frankie-eight-days/10x-hardware-engineer/boards/imx6ull-devboard/hardware/src/parts/Q_J_CR2032_BS_6_1/BAT-SMD_L28.5-W16.0-H5.5-LS31.3_CR2032-BS-6-1.STEP

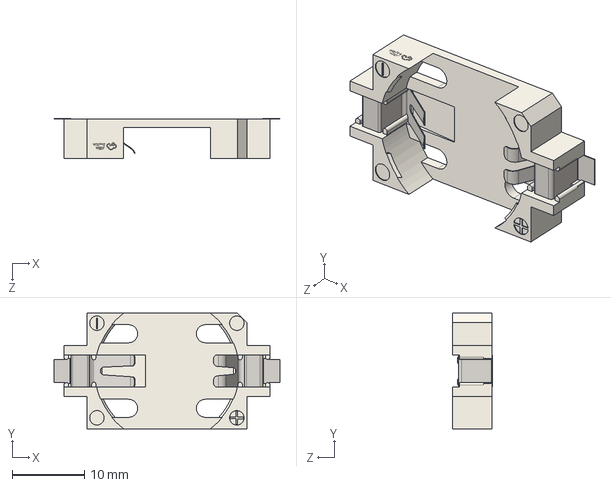
[picture p15: CAD file, 2026-05-05]
boards/imx6ull-devboard/hardware/src/parts/Q_J_CR2032_BS_6_1/BAT-SMD_L28.5-W16.0-H5.5-LS31.3_CR2032-BS-6-1.STEP
31.3 x 16.0 x 5.60 mm
