frankie-eight-days/10x-hardware-engineer/boards/imx6ull-devboard/hardware/src/parts/Samsung_Electro_Mechanics_CL21B102KBCNNNC/C0805_L2.0-W1.3-H1.3.step

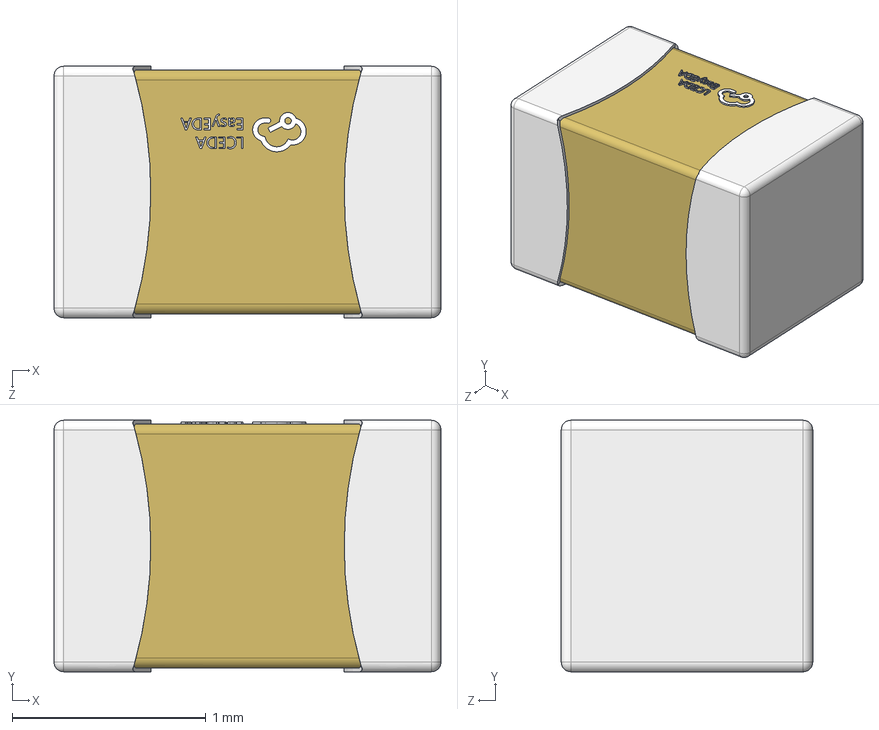
[picture p16: CAD file, 2026-05-05]
boards/imx6ull-devboard/hardware/src/parts/Samsung_Electro_Mechanics_CL21B102KBCNNNC/C0805_L2.0-W1.3-H1.3.step
2.00 x 1.30 x 1.30 mm
