frankie-eight-days/10x-hardware-engineer/boards/imx6ull-devboard/hardware/src/parts/Samsung_Electro_Mechanics_CL31A107MQHNNNE/C1206_L3.2-W1.6-H1.3.step

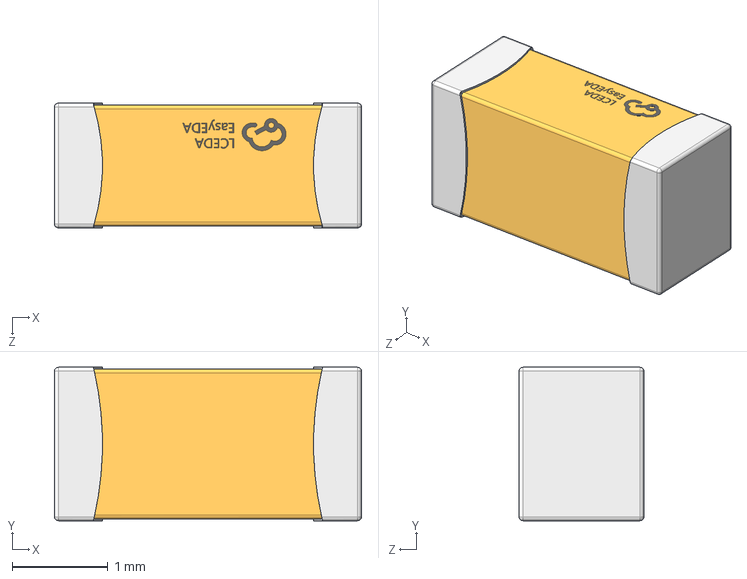
[picture p17: CAD file, 2026-05-05]
boards/imx6ull-devboard/hardware/src/parts/Samsung_Electro_Mechanics_CL31A107MQHNNNE/C1206_L3.2-W1.6-H1.3.step
3.20 x 1.60 x 1.30 mm
