frankie-eight-days/10x-hardware-engineer/boards/imx6ull-devboard/hardware/src/parts/Seiko_Epson_Q13FC13500004/FC-135R_L3.2-W1.5.STEP

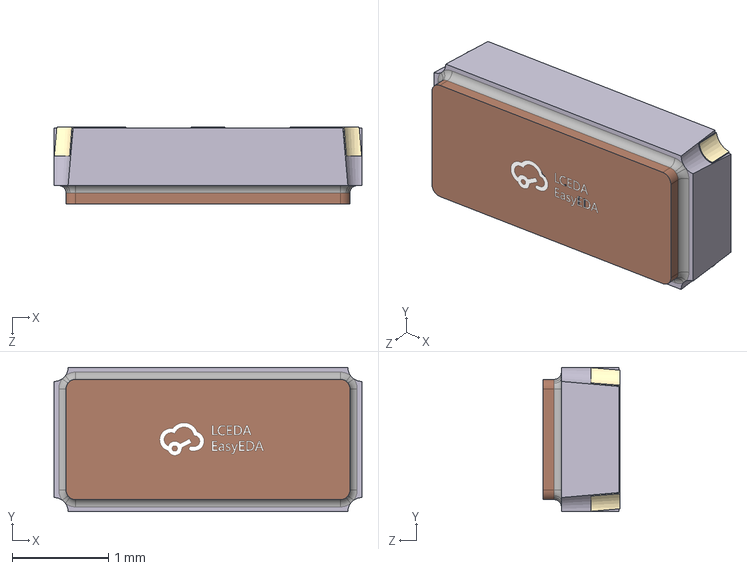
[picture p18: CAD file, 2026-05-05]
boards/imx6ull-devboard/hardware/src/parts/Seiko_Epson_Q13FC13500004/FC-135R_L3.2-W1.5.STEP
3.20 x 1.50 x 0.801 mm
