frankie-eight-days/10x-hardware-engineer/boards/imx6ull-devboard/hardware/src/parts/Sunlord_GZ2012D601TF/R0805_L2.0-W1.3-H0.6.step

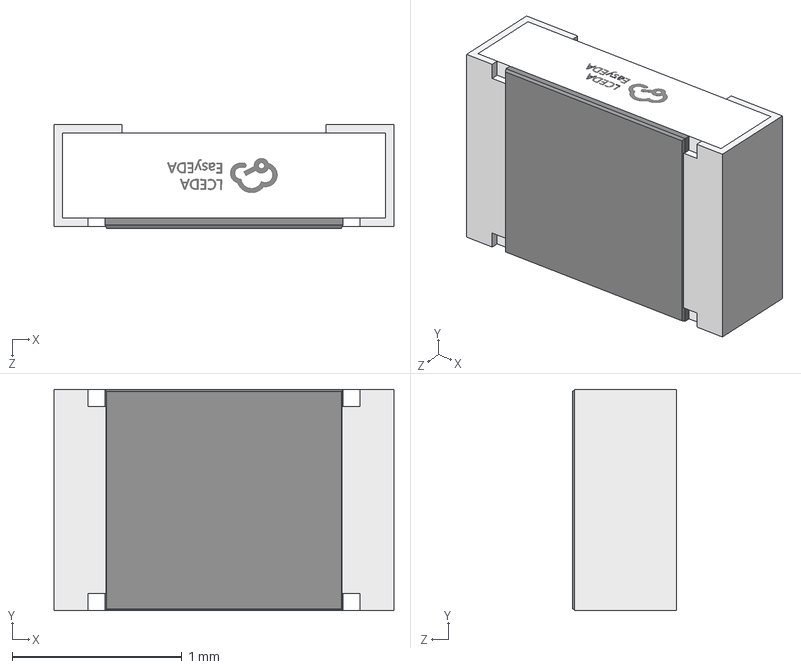
[picture p19: CAD file, 2026-05-05]
boards/imx6ull-devboard/hardware/src/parts/Sunlord_GZ2012D601TF/R0805_L2.0-W1.3-H0.6.step
2.00 x 1.30 x 0.61 mm
