frankie-eight-days/10x-hardware-engineer/boards/imx6ull-devboard/hardware/src/parts/SXN_SMNR5030_2R2N/IND-SMD_L5.0-W5.0-H1.2_SMNR5030.step

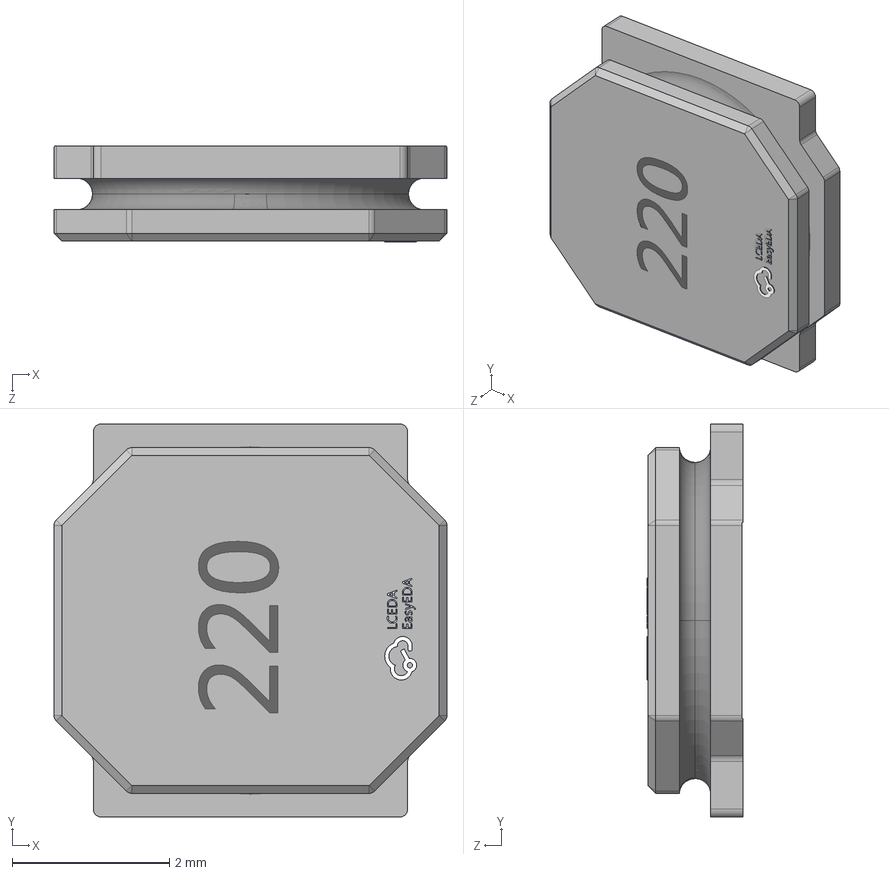
[picture p20: CAD file, 2026-05-05]
boards/imx6ull-devboard/hardware/src/parts/SXN_SMNR5030_2R2N/IND-SMD_L5.0-W5.0-H1.2_SMNR5030.step
5.00 x 5.00 x 1.22 mm
