frankie-eight-days/10x-hardware-engineer/boards/imx6ull-devboard/hardware/src/parts/TECH_PUBLIC_SRV05_4/SOT-23-6_L2.9-W1.6-H1.5-LS2.8-P0.95.step

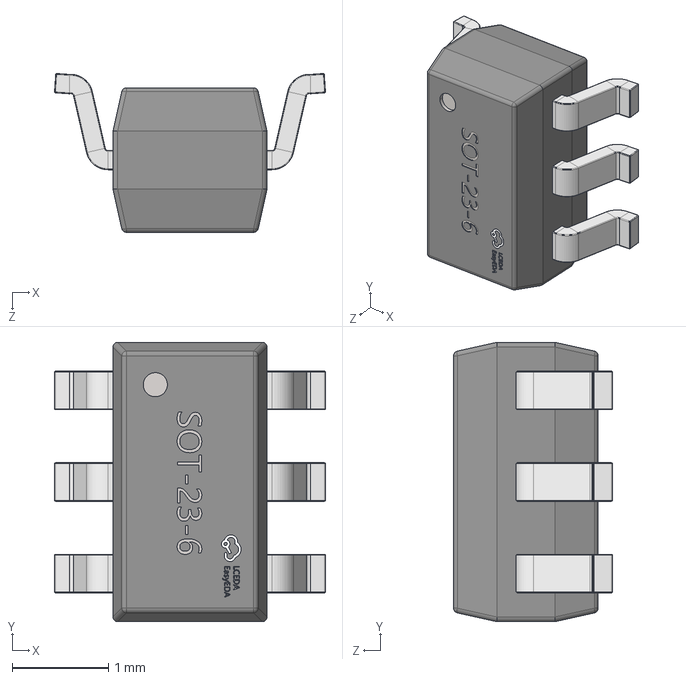
[picture p21: CAD file, 2026-05-05]
boards/imx6ull-devboard/hardware/src/parts/TECH_PUBLIC_SRV05_4/SOT-23-6_L2.9-W1.6-H1.5-LS2.8-P0.95.step
2.81 x 2.90 x 1.65 mm
