frankie-eight-days/10x-hardware-engineer/boards/imx6ull-devboard/hardware/src/parts/UNI_ROYAL_0603WAF1002T5E/R0603.STEP

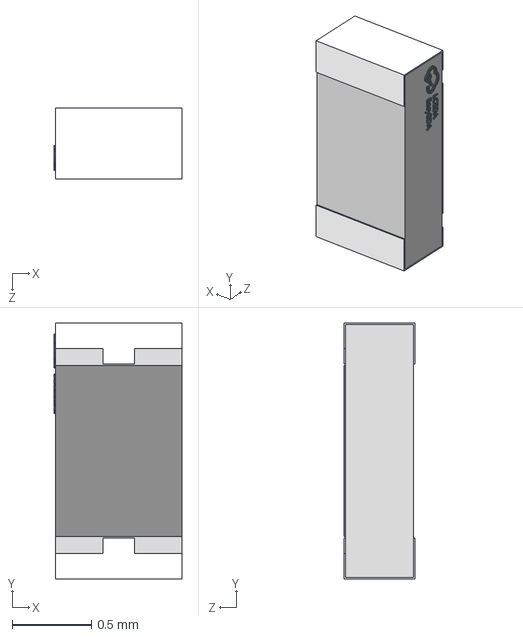
[picture p22: CAD file, 2026-05-05]
boards/imx6ull-devboard/hardware/src/parts/UNI_ROYAL_0603WAF1002T5E/R0603.STEP
0.81 x 1.62 x 0.45 mm
