frankie-eight-days/10x-hardware-engineer/boards/imx6ull-devboard/hardware/src/parts/WCH_CH340N/SOP-8_L4.9-W3.9-P1.27-LS6.0-BL-1.STEP

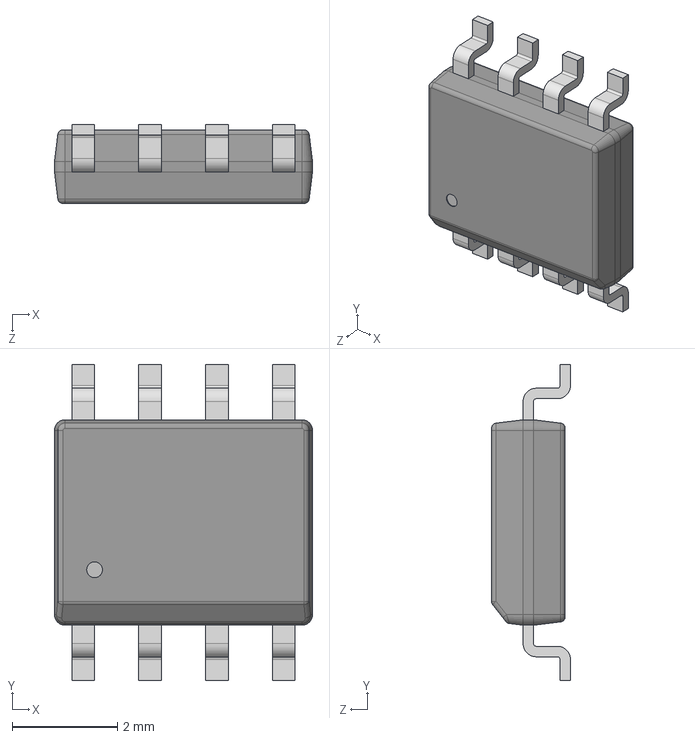
[picture p23: CAD file, 2026-05-05]
boards/imx6ull-devboard/hardware/src/parts/WCH_CH340N/SOP-8_L4.9-W3.9-P1.27-LS6.0-BL-1.STEP
4.90 x 6.00 x 1.50 mm
