frankie-eight-days/10x-hardware-engineer/boards/imx6ull-devboard/hardware/src/parts/Wcon_1310_1205G0M061CR02/CONN-SMD_1310-1205G0M061CR02.step

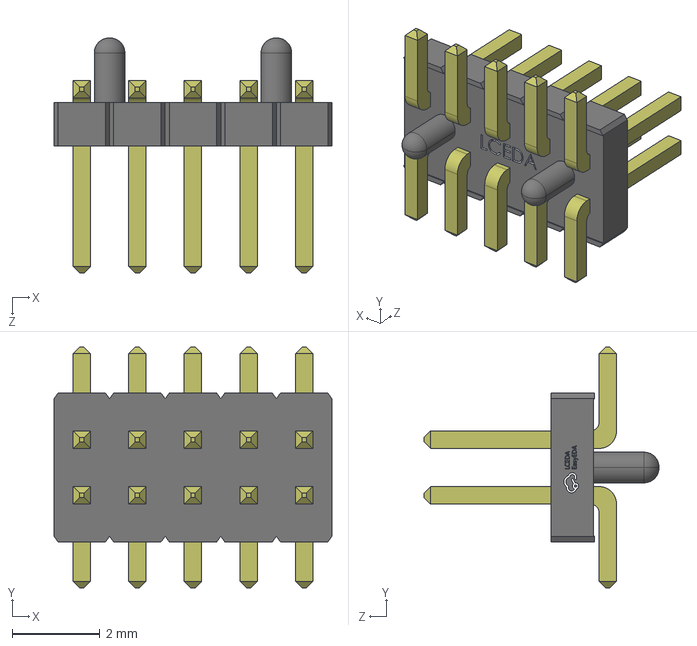
[picture p24: CAD file, 2026-05-05]
boards/imx6ull-devboard/hardware/src/parts/Wcon_1310_1205G0M061CR02/CONN-SMD_1310-1205G0M061CR02.step
6.35 x 5.50 x 5.37 mm
