frankie-eight-days/10x-hardware-engineer/boards/imx6ull-devboard/hardware/src/parts/XKB_Connectivity_TS_1187A_B_A_B/SW-SMD_4P-L5.1-W5.1-P3.70-LS6.5-TL_H1.5.STEP

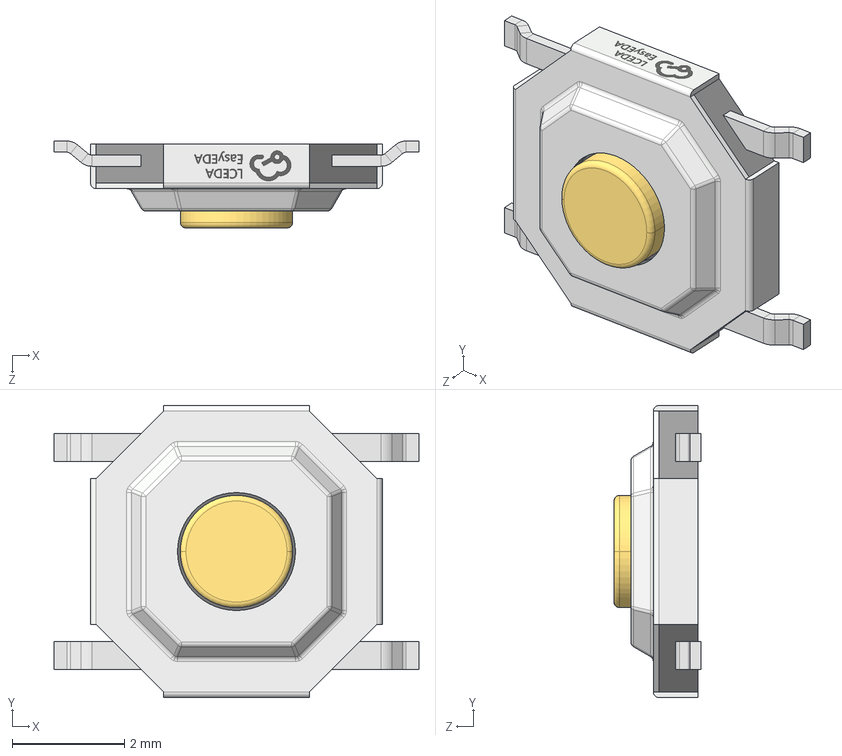
[picture p25: CAD file, 2026-05-05]
boards/imx6ull-devboard/hardware/src/parts/XKB_Connectivity_TS_1187A_B_A_B/SW-SMD_4P-L5.1-W5.1-P3.70-LS6.5-TL_H1.5.STEP
6.50 x 5.20 x 1.55 mm
