frankie-eight-days/10x-hardware-engineer/boards/imx6ull-devboard/hardware/src/parts/YAGEO_CC0603KRX7R9BB104/C0603_L1.6-W0.8-H0.8.step

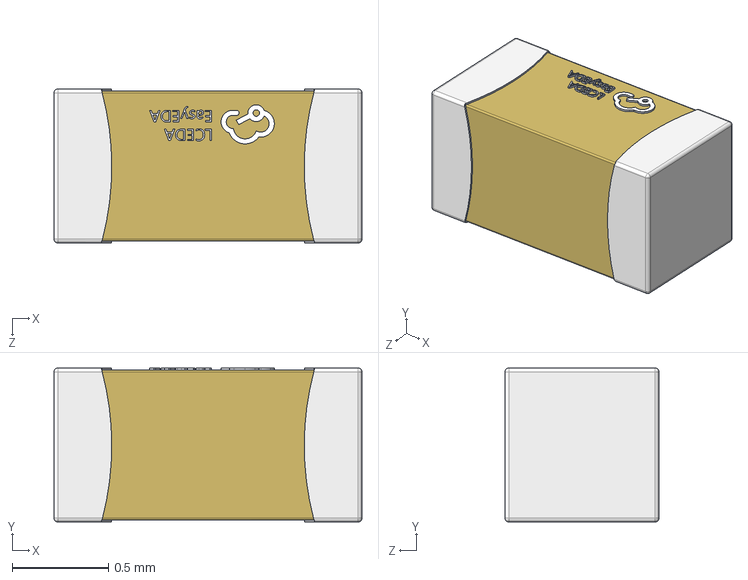
[picture p26: CAD file, 2026-05-05]
boards/imx6ull-devboard/hardware/src/parts/YAGEO_CC0603KRX7R9BB104/C0603_L1.6-W0.8-H0.8.step
1.60 x 0.8 x 0.8 mm
