frankie-eight-days/10x-hardware-engineer/boards/imx6ull-devboard/hardware/src/parts/Yangxing_Tech_X322524MOB4SI/OSC-SMD_L3.2-W1.5-H0.8.STEP

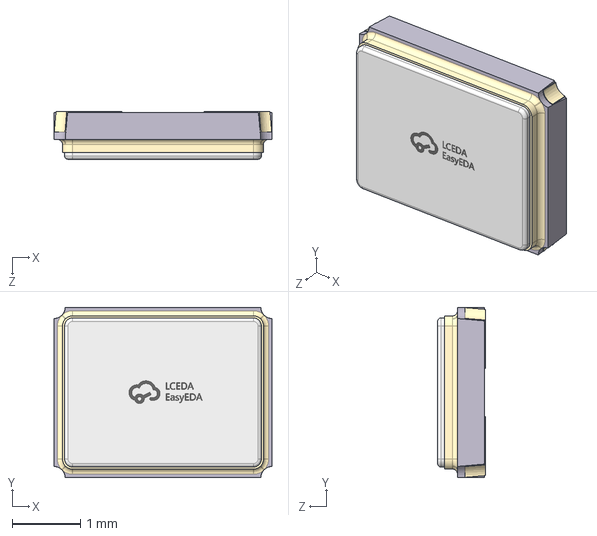
[picture p27: CAD file, 2026-05-05]
boards/imx6ull-devboard/hardware/src/parts/Yangxing_Tech_X322524MOB4SI/OSC-SMD_L3.2-W1.5-H0.8.STEP
3.20 x 2.50 x 0.701 mm
